Saqoosha/Canopy-MacroPad/case/out/choc/bottom.png

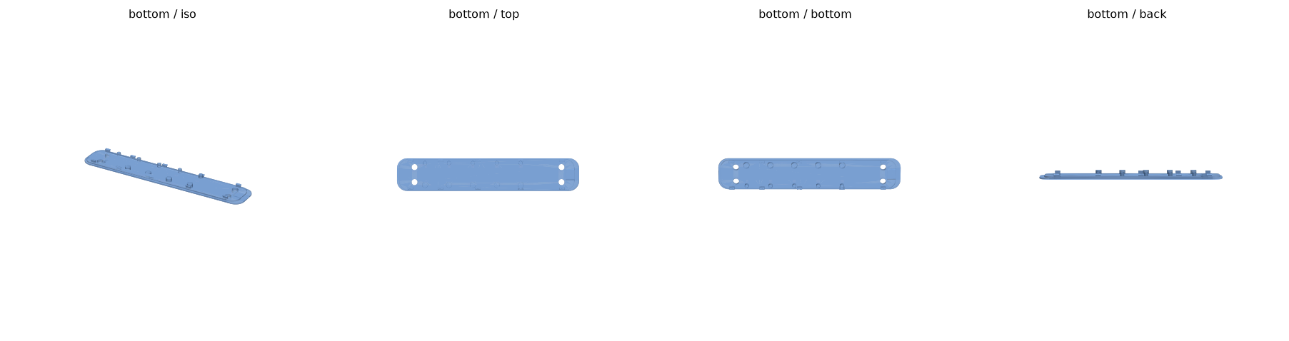
case/out/choc/bottom.png
