Saqoosha/Canopy-MacroPad/case/out/choc/coupon-clear.png

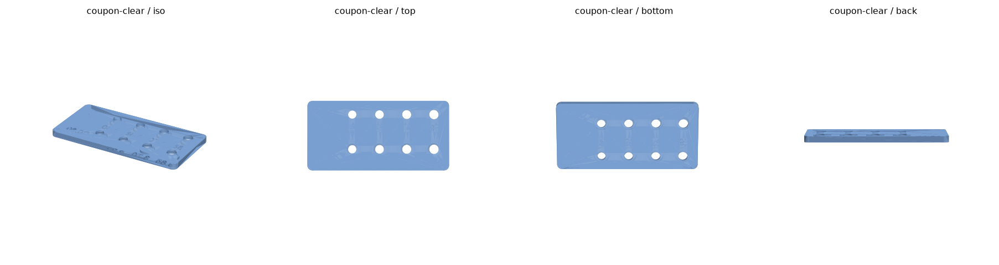
case/out/choc/coupon-clear.png
