Saqoosha/Canopy-MacroPad/case/out/choc/keycap.png

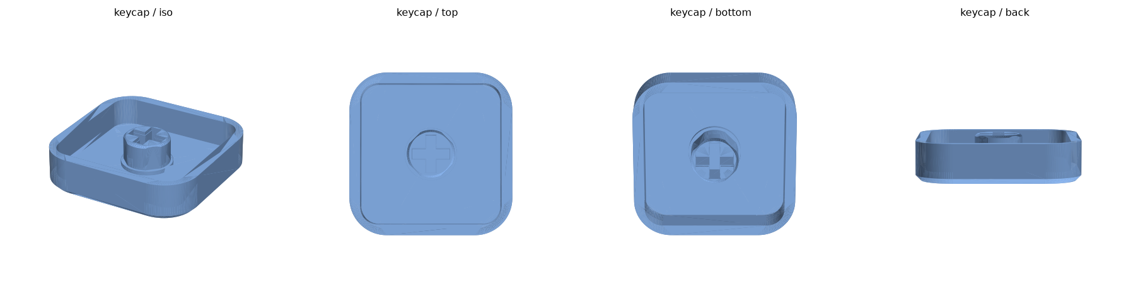
case/out/choc/keycap.png
