Saqoosha/Canopy-MacroPad/case/out/choc/product.png

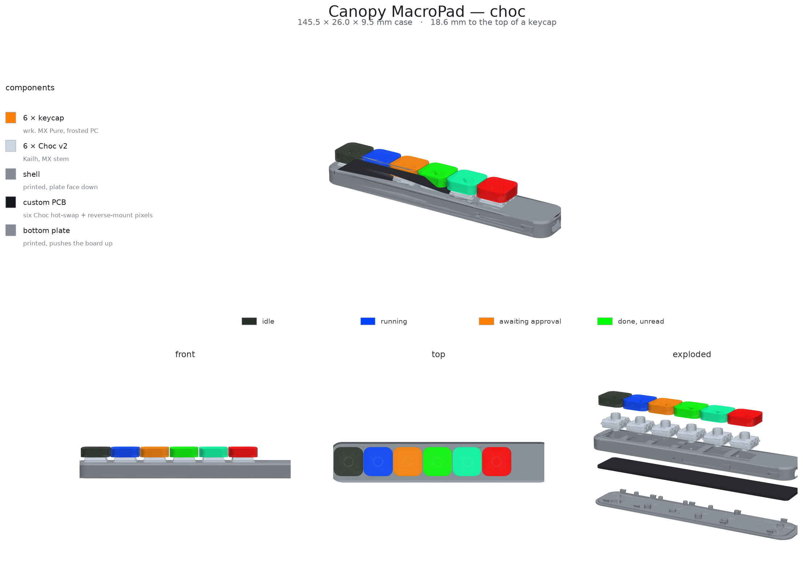
case/out/choc/product.png
