Saqoosha/Canopy-MacroPad/pcb/out/board-free.png

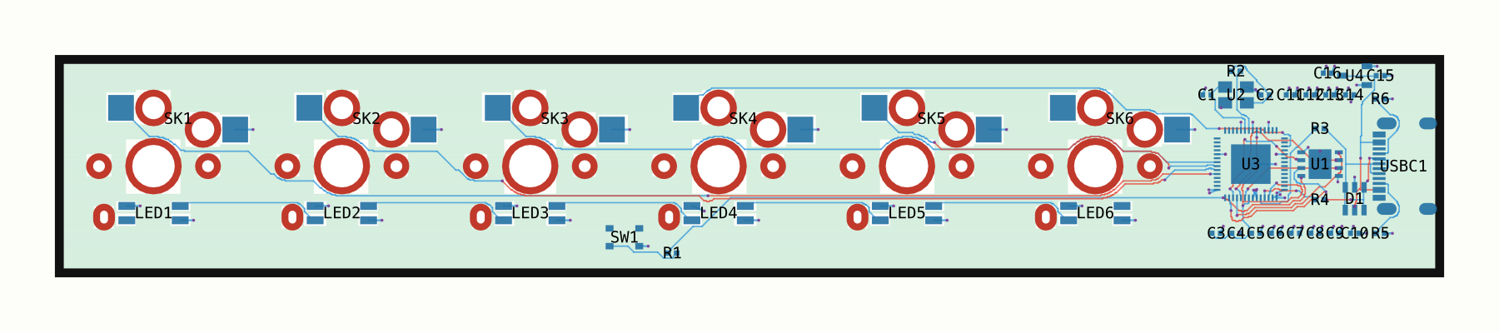
pcb/out/board-free.png
