Saqoosha/Canopy-MacroPad/pcb/out/board-large.png

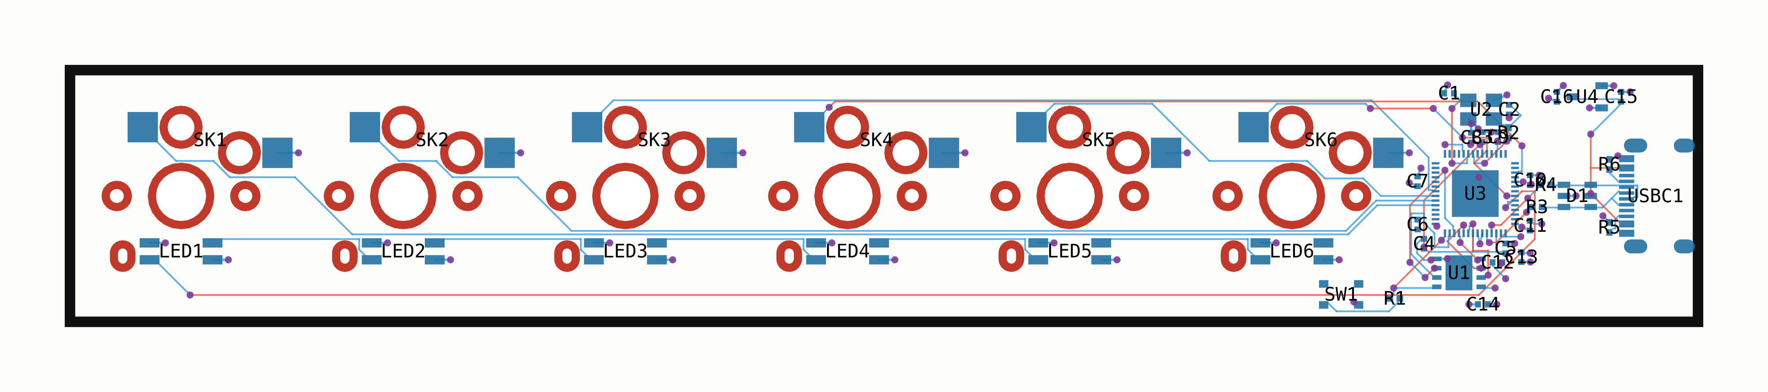
pcb/out/board-large.png
