Saqoosha/Canopy-MacroPad/pcb/out/mcu-crop.png

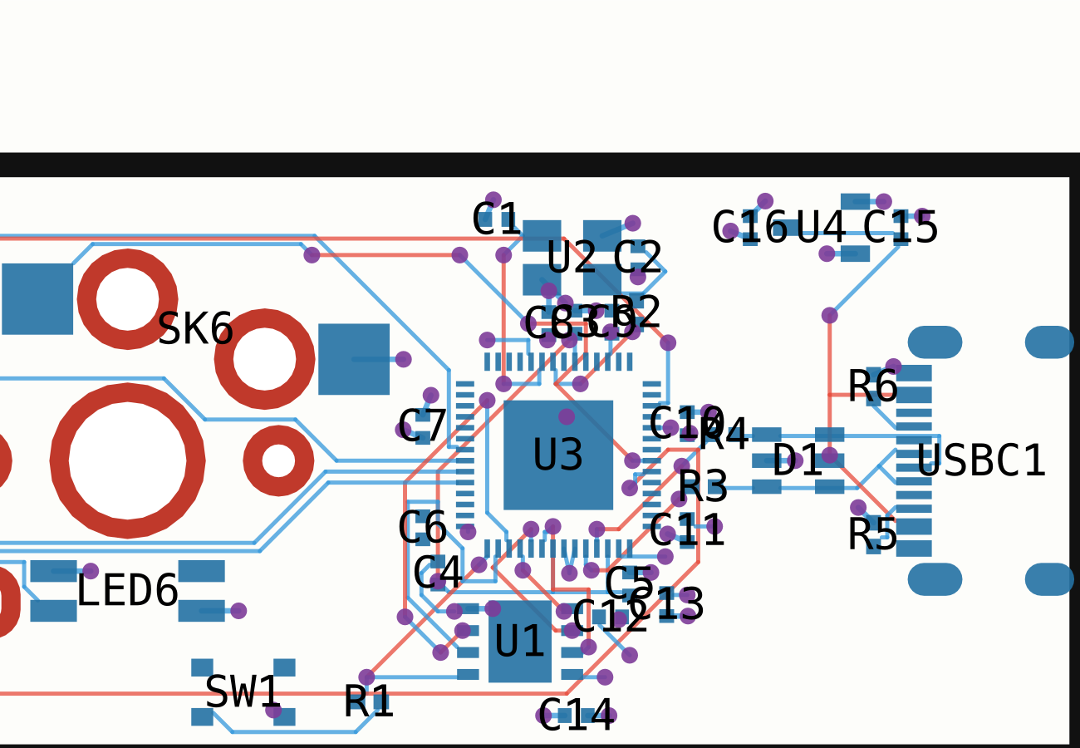
pcb/out/mcu-crop.png
