Saqoosha/Canopy-MacroPad/case/out/inline/coupon.step

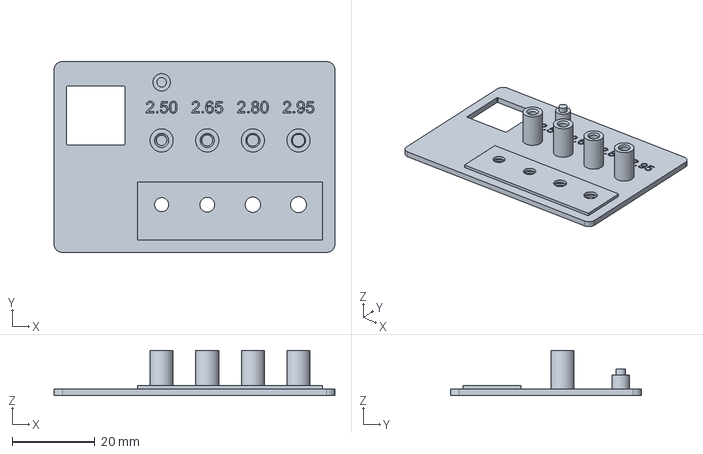
[picture p29: CAD file, 2026-08-14, an earlier design]
case/out/inline/coupon.step
67.8 x 46.0 x 10.9 mm
