Saqoosha/Canopy-MacroPad/case/out/stacked/shell.step

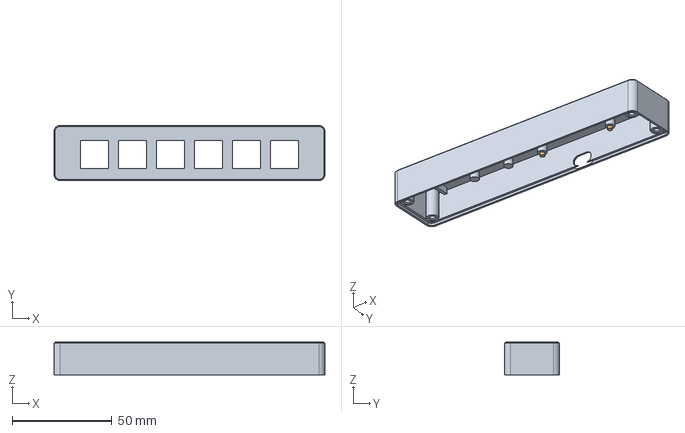
[picture p30: CAD file, 2026-08-14, an earlier design]
case/out/stacked/shell.step
135.7 x 27.6 x 16.3 mm
