Saqoosha/Canopy-MacroPad/docs/wiring/boards.jpg

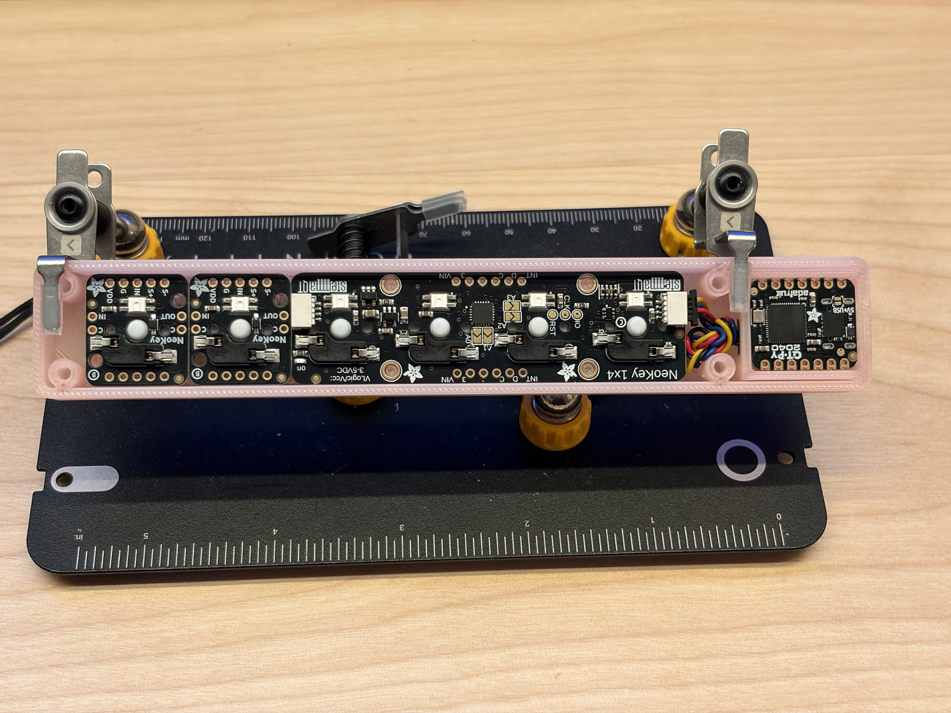
docs/wiring/boards.jpg
