Saqoosha/Canopy-MacroPad/firmware/code.py

"""Canopy MacroPad — main firmware.

The device is deliberately dumb: it reports key edges and paints the
colors it is told to paint. All meaning (which pane, which status, when
to pulse) lives in the host. That split is what lets the same wire
protocol survive the move to BLE later.

Wire protocol, line-delimited ASCII on usb_cdc.data.

  host -> device
    C <idx> <rrggbb>   set key idx to that color, e.g. `C 0 ff8000`
    S <idx> <rrggbb> [ms] [floor]
                       pulse that color, eased by `PULSE_CURVE`. `ms` is the full
                       period (min 100), `floor` is the percentage the
                       dip bottoms out at, 0-100: 0 reads as an alert,
                       50 as a slow breath that says "alive" without
                       asking for attention. Defaults: 2500 ms and 0.
                       Both are clamped silently.
    B <0-100>          global brightness
    X <ms>             crossfade duration for C and S, default 500
    P                  ping
    R                  reset: all keys off, immediately

  device -> host
    HELLO <ver> <keys> sent when a host opens the data port
    PONG <ver> <keys>  reply to P
    K <idx> <0|1>      key idx pressed (1) / released (0)
    ERR <msg>          a command could not be handled

`C` and `S` drop out-of-range key indices in silence; the host may paint
before it has learned the key count.

Every change of color or floor is crossfaded (except `R` and a host
disconnect, which are immediate), so a state change reads as
a state change and not as an alarm. Solid is modelled as a pulse whose
floor is 100%, which is what lets one interpolation cover all four
transitions -- solid to solid, solid to pulsing, pulsing to solid, and
pulsing to pulsing -- with no special cases.

**A pulsing key keeps its phase when only its color or floor changes.**
Resetting it would drop the breath back to its trough, and "the heartbeat
stopped" reads louder than "the urgency changed", which is the opposite
of what happened. Phase restarts only when a solid key starts pulsing, or
when the period itself changes.

Nothing else is written to the data port, and debug output goes to the
console port (plain `print`) which the host does not read — with one
exception. If `boot.py` did not take effect there is no data port, and
this falls back to the console, where protocol lines then share a stream
with the REPL banner and any tracebacks. The host is told so explicitly:
it receives `ERR no-data-cdc-check-boot-py` right after `HELLO`.
"""

import array
import math
import os
import sys
import time

import microcontroller
import usb_cdc

# adafruit_neokey and neopixel live in CIRCUITPY/lib, so they are the
# imports that can be missing -- a board flashed without the bundle, or
# with one for the wrong CircuitPython major. That is the same class of
# operator error as a missing Qwiic cable, which this firmware goes to
# real trouble to survive; at module scope they instead raise straight
# to the REPL and produce the silent brick everything else here is built
# to avoid. Imported inside the setup guards below instead.
#
# Two guards rather than one, because the two halves of the keypad fail
# independently now: a missing `neopixel` must not cost the NeoKey its
# LEDs, and a missing Qwiic cable must not cost the breakouts theirs.
NeoKey1x4 = None
NeoPixel = None

# 1: C / B / P / R
# 2: adds S (device-side eased pulse)
# 3: adds X, crossfades every C/S, and holds phase across a colour change
PROTOCOL_VERSION = 3

# Two boards run this file and they are not the same shape. The QT Py
# build is two Adafruit 4978 breakouts on GPIO plus a NeoKey on I2C; the
# custom PCB is six switches straight to GPIO and one six-pixel chain.
#
# They cannot share one pin table even though they share pin *numbers*.
# The PCB was laid out against the QT Py's broken-out GPIO on purpose, so
# the same eleven numbers are available on both -- but GPIO3 is the
# breakouts' pixel line on one board and KEY0 on the other. Every
# difference between the two devices lives in this table.
#
# Pins are GPIO **numbers**, resolved through `microcontroller.pin`, not
# names through `board`. `board` carries a per-build name table, and the
# QT Py's names are simply absent from the generic build the PCB runs --
# measured on the real board, not assumed: `[n for n in ('MOSI', 'MISO',
# 'SCK', 'TX', 'RX', 'SDA', 'SCL') if hasattr(board, n)]` returns `[]`
# there. `microcontroller.pin.GPIOn` is the chip's own numbering and is
# on every RP2040 build.
PROFILES = {
    # Adafruit QT Py RP2040. Keys 0-1 are the two breakouts, keys 2-5 the
    # NeoKey. All three GPIO sit on the QT Py's 3V/GND edge, so the
    # harness does not have to cross the board.
    "qtpy": {
        "gpio_keys": (4, 6),                # MISO, SCK
        "gpio_pixel": 3,                    # MOSI
        "pad_addresses": (0x30,),
        # 50 Hz, and no dithering at that rate -- see `PAINT_HZ`. Four of
        # this board's six pixels live behind seesaw, so a paint is I2C
        # traffic competing with the key scan for the same bus, and the
        # NeoKey's own comment upstream is about exactly that cost.
        "paint_hz": 50,
        # No dithering at 50 Hz: the table beside `DITHER` measures it as
        # worse than none.
        "dither": False,
    },
    # The custom PCB. Six switches on GPIO in the board's physical key
    # order, one chain of six pixels, and no I2C anywhere on the board --
    # so the whole I2C half below is skipped rather than failing.
    "pcb": {
        "gpio_keys": (3, 4, 6, 20, 5, 24),
        "gpio_pixel": 25,
        "pad_addresses": (),
        # 200 Hz, which is what buys the dithering below. Every pixel is
        # on one bit-banged GPIO chain: six of them is ~260 us per show,
        # so 200 Hz costs about 5% of wall time and no bus at all.
        "paint_hz": 200,
        # The loop achieves about 148 Hz of that with six keys pulsing, and
        # the flag is True on the strength of the lit board rather than of
        # the request: at that rate a 50/50 dither alternates near 74 Hz,
        # and every depth from 67% down was invisible on a static ladder.
        "dither": True,
    },
}

# Which profile, decided by which CircuitPython **binary** is running.
#
# That is not the detection this file forbids, and the difference is the
# whole reason this one is allowed to be automatic. Whether a breakout is
# *wired* is electrically unknowable -- an absent one and a present one
# nobody is pressing are both pulled high, with no readback on the pixel
# line and no capacitive sense on an RP2040 -- so that question was
# always a human's to answer. Which build you booted is a compile-time
# string, and there is no guess in reading it.
#
# `settings.toml`'s `MPAD_BOARD` overrides the table, and is the answer
# of record for a board whose build name is not in it. The PCB currently
# runs a stock `raspberry_pi_pico` build: a name it does not own, that an
# actual Pico would also answer to, and that stops matching the day the
# board gets a definition of its own.
#
# An unrecognised answer gets **no** fallback profile. A wrong guess
# renumbers every key silently, which is the one failure this file is
# built to prevent, so it comes up with no hardware at all and says so.
# Both strings were read off their own board's REPL, not taken from a
# board definition: `print(sys.implementation._build)` answers
# 'raspberry_pi_pico' on the built PCB and 'adafruit_qtpy_rp2040' on the
# QT Py. Worth re-reading after a CircuitPython upgrade, and the failure
# if one ever stops matching is the safe one -- that board comes up with
# `HELLO <ver> 0` and `ERR board ...` rather than with wrong pins, and
# `MPAD_BOARD` in settings.toml fixes it without a reflash.
BUILD_TO_PROFILE = {
    "adafruit_qtpy_rp2040": "qtpy",
    "raspberry_pi_pico": "pcb",
}
# Read through `getattr` because `_build` is a private attribute, and this
# line is at module scope where an AttributeError is the silent brick --
# CircuitPython stops `code.py`, the port goes quiet, and from the host
# that is indistinguishable from a board that never booted. A release that
# renames or drops it must land in the failure this file already has a
# path for: no profile, `ERR board`, and a device that still talks.
# `os.getenv` is not wrapped, deliberately -- it is public API, and
# guarding everything that could theoretically move is how a guard stops
# meaning anything.
_build = getattr(sys.implementation, "_build", None)
_forced = os.getenv("MPAD_BOARD")
BOARD_PROFILE = _forced or BUILD_TO_PROFILE.get(_build)
if BOARD_PROFILE in PROFILES:
    board_error = None
    _profile = PROFILES[BOARD_PROFILE]
else:
    board_error = "{} {!r} is not one of {}".format(
        "MPAD_BOARD" if _forced else "build",
        _forced or _build,
        "/".join(sorted(PROFILES)))
    _profile = {"gpio_keys": (), "gpio_pixel": None, "pad_addresses": (),
                "paint_hz": 50, "dither": False}

# The I2C addresses of the NeoKey boards, in physical left-to-right key
# order. This tuple is the single source of truth for how many boards
# exist -- deriving it the other way round (a count that slices a longer
# address list) silently clamps instead of failing. A second board needs
# its A0 jumper bridged on the back to answer 0x31. Empty on a board with
# no I2C keypad, and then nothing here is imported, addressed or reported
# on.
PAD_ADDRESSES = _profile["pad_addresses"]
KEYS_PER_PAD = 4
SEESAW_KEYS = KEYS_PER_PAD * len(PAD_ADDRESSES)

# The keys read straight off GPIO, in physical left-to-right order. They
# carry no seesaw, so there is nothing to address and nothing to
# enumerate -- which is why this is the half that cannot fail to come up.
# On the QT Py that is keys 0-1 and they come *before* the NeoKey's four;
# on the PCB it is all six and there is no other half.
#
# The switch wiring differs between the boards and only one of them has a
# margin worth watching. Each 4978 breakout puts its switch in series
# with a 1N4148 running SWITCHA to SWITCHC, and SWITCHC goes to ground,
# so a press pulls its input low *through the diode*. The forward drop at
# the ~55 uA an internal pull-up supplies is about 0.45 V, under the
# RP2040's 0.8 V V_IL but not by a wide margin: a key that reads
# permanently pressed is the symptom of that number being wrong, and an
# external pull-up is the fix. The PCB's switches go straight to ground
# with no diode in the way, so they have no such margin to lose.
#
# Resolved against `microcontroller.pin` inside the setup guard rather
# than here. A number missing from it would be an AttributeError at
# module scope, which is the silent brick again -- and a wrong-board
# flash is exactly when you want the serial half still talking.
GPIO_KEY_GPIO = _profile["gpio_keys"]
GPIO_PIXEL_GPIO = _profile["gpio_pixel"]
GPIO_KEYS = len(GPIO_KEY_GPIO)

# Index order is physical, left to right, and on the QT Py the case
# decided it rather than this file: the breakouts sit to the *left* of
# the NeoKey, for reasons of plug clearance and cable reach that
# `case/params.py` owns and states with its own numbers
# (`BREAKOUT_ORIGINS_LOCAL`). Restating one of them here is how a number
# gets carried away from what makes it true, so it is not restated.
#
# So on the QT Py the GPIO pair is 0-1 and the NeoKey is 2-5; on the PCB
# the GPIO six are 0-5 and `SEESAW_BASE` lands past the end and is never
# used. These two constants are the only place that knows which way round
# it goes.
GPIO_BASE = 0
SEESAW_BASE = GPIO_KEYS

# Derived from the profile, not from what enumerated at runtime. Key 2 is
# key 2 whether or not the NeoKey answered: the host maps index to pane,
# so letting the boards renumber when the Qwiic cable is out would
# quietly focus the wrong session.
#
# Both real profiles come to 6, by different sums -- 2 + 4 on the QT Py,
# 6 + 0 on the PCB -- so a missing NeoKey shows up as `HELLO <ver> 6`
# plus `ERR i2c ...` and the host paints keys 2-5 into a board that is
# not there. Writes to absent hardware are dropped in silence, the same
# way an out-of-range index already is.
#
# `HELLO <ver> 0` is reachable again, and means one thing only: this
# firmware does not know what board it is on. It arrives with `ERR board
# ...`, and it is the honest report -- claiming six keys that resolve to
# no pins would be a positive claim of health, which is worse than
# silence.
NUM_KEYS = SEESAW_KEYS + GPIO_KEYS

# Full brightness is genuinely painful to sit next to, but going too dim
# costs 8-bit steps: at 30% a deep pulse has only a handful of distinct
# values near its floor and visibly stalls there. 60% measured as the
# point where the fade stays smooth without being glaring. The host can
# override this at runtime with `B`.
#
# Measured on a lit board, and the number stands -- but for a reason the
# original note did not have. `DITHER` buys steps back above
# `DITHER_FLOOR`, and separately the board says a one-level step stops
# being visible around value 2 anyway. So the low end is not as bad as
# this comment once implied, and 60 is no longer a floor forced by
# quantisation. It is still what idle's white balance was measured at,
# which is the reason not to move it casually.
DEFAULT_BRIGHTNESS = 0.6

# All timing is integer nanoseconds. `time.monotonic()` returns a float
# whose precision decays with uptime -- on a single-precision build the
# step near `now` grows past both thresholds below in a day or two --
# 15 ms is the ulp somewhere past 2^17 seconds -- and this is a device
# that lives plugged into a desk. The failure
# is silent and awful: the debounce window stops measuring anything, so
# one press reports as several and the wrong pane gets focused.
DEBOUNCE_NS = 15_000_000       # 15 ms

# How often the LEDs are repainted, and it is a per-board number because
# it buys different things on the two boards. It is the pulse's sample
# rate, and -- at 200 Hz and above -- the carrier the dithering below
# rides on.
#
# **It is a request, not the achieved rate.** `POLL_INTERVAL_S` is 5 ms so
# 200 Hz is the arithmetic ceiling, but the loop measured **148 Hz** with
# six keys pulsing -- a 26% shortfall. Which is why whether to dither is a
# separate field in the profile rather than a comparison against this
# number: a comparison would be deciding on a rate the board does not
# reach. What was actually judged, on the lit board at 148 Hz, is recorded
# beside each profile's flag.
PAINT_HZ = _profile["paint_hz"]
PULSE_STEP_NS = 1_000_000_000 // PAINT_HZ
# Temporal dithering is only switched on where the paint rate can carry
# it, and 200 Hz is not a round number -- it is where the measurement
# crosses over. Error-diffusing at 50 Hz is *worse than not dithering*,
# because the dither's own alternation then lands inside the band the eye
# sees as flicker rather than above it. Simulated against the real
# quantiser, error energy in the visible 5-30 Hz band, in LSB rms, for a
# gamma-2.0 breath at floor 0.15:
#
#     brightness   today@50   dither@50   @100    @200    @400
#     0.10            0.254      0.396   0.230   0.084   0.031
#     0.15            0.237      0.378   0.237   0.075   0.029
#     0.60            0.347      0.390   0.198   0.082   0.037
#
# So 50 Hz loses, 100 Hz draws, and 200 Hz wins by 3x. A board that
# cannot afford 200 Hz must not dither at all, which is why this is a
# threshold and not a preference.
# Read from the profile rather than derived as `PAINT_HZ >= 200`, which is
# what this line used to say and was a small lie: `PAINT_HZ` is the rate
# the loop *asks* for and the PCB achieves about 148 of it, so the
# comparison passed on a board that misses its own stated bar. The
# threshold above is still the reason each flag is set the way it is; what
# changed is that the flag records a decision instead of pretending to
# derive one, and the profile carries the measurement beside it.
DITHER = _profile["dither"]

# Below this output value a channel is rounded rather than dithered, and
# it is the second half of the threshold above -- 200 Hz is necessary and
# is not sufficient. Both numbers came off the lit board, on static
# ladders where nothing but the dither could move.
#
# What the eye is judging is the dither's *depth*, one level as a share
# of the light there, against the rate its pattern happens to run at.
# Error diffusion holds one value for 1/fraction frames, so at 200 Hz a
# fraction of 0.1 alternates at 20 Hz. Painting faster raises that -- 400
# Hz would give 40 Hz -- but then a fraction of 0.05 alternates at 20 Hz
# instead. The rate cannot be bought out of this, because the fraction
# can always be smaller.
#
#   depth   1 LSB on   at 100 Hz   at 20 Hz
#   100%    value 1    calm        flickers
#    50%    value 2    calm        flickers
#    33%    value 3    calm        faint, still there
#    20%    value 5    calm        calm
#    11%    value 9    calm        calm
#
# So 5 is where the worst rate stops being visible. 4 is the untested
# boundary and 5 is inside it.
#
# **That derivation assumes the LED is linear, and it is not.** Keys held at
# 0/1/2/3/4/5 side by side on the real board: 0 to 1 is a different world, 1
# to 2 is plainly visible, and 2/3/4/5 cannot be told apart at all. Only the
# first two steps are visible, so 5 is conservative rather than correct --
# and the arithmetic above, which reasons about "one level as a share of the
# light", is answering a question the part does not obey. Left at 5 because
# nothing in service goes near it (see below), not because the number was
# re-derived. What this buys back is everything above
# it; below it the levels were never recoverable by any temporal trick,
# and rounding at least fails quietly. A dither there is not a smoother
# value, it is a light switching on and off.
DITHER_FLOOR = 5.0

# Adds roughly 5 ms plus the scan and paint themselves on top of the
# 15 ms debounce, so a press reaches the host in ~20 ms. The debounce
# dominates; this only decides how much is added to it.
POLL_INTERVAL_S = 0.005

# The pulse lives here rather than on the host. A square blink is one
# command per half period and could sit on the host happily; a sine fade
# is ~50 updates a second, which is a silly thing to push down a wire and
# would stutter on any host hiccup. Keeping it local also means the pulse
# is already where it has to be when this moves to BLE.
#
# A pulse is timed from the moment its command arrives, so a key entering
# a state fades up from its floor and the transition itself is visible.
# An earlier revision also added a fixed per-key phase offset, to stagger
# keys told to pulse in the same instant. The two are not compatible: an
# offset that is non-zero at t=0 is exactly a key that does not start at
# its floor, and with four keys it put key 2 at full brightness on its
# very first frame. Starting at the floor won, because the key it broke
# is whichever one is holding the approval state -- nothing here maps a
# key index to a pane state, so it could be any of them. Keys whose states change at different
# moments still drift apart on their own.
#
# 2.5 s, chosen on a lit board against 2/3/4/5/6/8 s shown on the six keys
# at once. 2 s is 30 breaths a minute, outside the 12-20 a resting adult
# does, and a photodiode capture of a real MacBook sleep light measured
# about 12; this lands at 24, which is slower than the 2 s it replaces and
# still quick enough that a deep pulse reads as a request rather than as
# scenery. Every state uses it and only the floor changes.
#
# The host sends its own period with every `S`, so this is what a host that
# omits one gets, not what the pad normally runs. Canopy sends 2500.
DEFAULT_PULSE_PERIOD_MS = 2500
# `PULSE_GAMMA` shapes nothing any more. It is the exponent of the cosine
# family the curve below replaced, kept because that family's runner-up is
# one line away and because the number itself was earned: 1.5, picked on a
# lit board from a sweep of 1.0/1.2/1.4/1.6/1.8/2.0 carried on the six keys
# at once.
#
# What that sweep settled, and it is worth keeping because the first
# explanation of it was half wrong. A raw sine (gamma 1.0) reads as "the
# bottom is short and the top is long" -- it lingers exactly where the eye
# is least able to see a change. Gamma 2.0 reads as a pause at the bottom,
# because level-minus-floor goes as t^4 there against t^2 at 1.0, so the
# lowest 1% of the swing lasts 410 ms of a 2 s breath instead of 128. Both
# ends are wrong and the answer was between them.
#
# The old note in this place blamed that pause on there being few 8-bit
# levels at low brightness. Both facts are real and they are not cause and
# effect: the freeze is the two **meeting**, 410 ms of dwell spanning under
# 2 LSB. Dithering is the right instrument for that half and the note was
# right to name it; what it got wrong was calling it cheap. It costs a 4x
# paint rate (`DITHER`), below 200 Hz it makes the pulse worse, and below
# `DITHER_FLOOR` no rate saves it at all.
#
# And the whole quantisation half turned out not to happen in service. The
# deepest breath Canopy sends bottoms out at 7.7 of 255 in its faintest lit
# channel, where a one-level step stopped being visible around 2 -- measured
# on the board, keys held at 0/1/2/3/4/5 side by side. Everything above was
# found at brightness 15 with a floor of 0, which is outside the envelope
# the pad is ever driven in.
PULSE_GAMMA = 1.5

# The breath, precomputed at boot. Not from `PULSE_GAMMA` -- that constant
# belongs to the cosine family this replaced; see its own note above.
#
# The shape is `exp(sin)`: `(e^sin(x) - 1/e) / (e - 1/e)`, normalised and
# phase-shifted to start at its minimum. Narrow peak, wide trough -- the
# dwell sits at the bottom of the breath where a raw sine puts it at the
# top, and the top is exactly where the eye is least able to see a change.
# Traced to a 2010 comment by Adam Shea, popularised by Sean Voisen in
# 2011; Shea's stated reason was correcting the log response of
# LED->eye->brain rather than modelling breathing, and the curve is
# exactly time-symmetric about its peak whatever the folklore says.
#
# Chosen on a lit board against five others shown side by side on the six
# keys at once -- a plain triangle, FastLED's `quadwave` and `cubicwave`,
# `sine^1.5`, and the Gaussian fitted to a real MacBook sleep light -- all
# sharing colour, floor, phase and brightness so only the curve differed.
# A gamma sweep over the cosine ran the same way first: 1.0 read as "the
# bottom is short and the top is long", 2.0 as a pause at the bottom, and
# 1.5 was the best of that family before this beat it.
#
# `PULSE_GAMMA` no longer shapes anything -- it belongs to the cosine
# family this replaced. It is kept only because `sine^1.5` is one line
# away and was the runner-up:
#
#     _raw = [((1 - math.cos(2 * math.pi * _i / _CURVE_STEPS)) / 2)
#             ** PULSE_GAMMA for _i in range(_CURVE_STEPS)]
#
# The **table** is a speed change with no effect on the shape. `math.cos`
# and `** PULSE_GAMMA` ran once per key per frame and measured as the
# largest single cost in the loop, and the index is integer arithmetic so
# the float divide goes with them.
#
# 512 is not a round number, it is the smallest power of two finer than a
# frame. A table adds a visible stair only when its steps are coarser than
# the frames sampling it, so the comparison that decides the size is
# against the loop rate rather than against the eye:
#
#     table    step     biggest jump      steps per frame
#     entries  apart    between entries   at 148 Hz (6.76 ms)
#      256     7.81 ms      3.61 LSB           0.9   <- coarser than a frame
#      512     3.91 ms      1.81 LSB           1.7
#
# The biggest change one frame to the next is 3.13 LSB at 148 Hz, so at 512
# the table's own step is already the smaller of the two and contributes no
# hold the frames did not already have. At 256 it is the larger, and would.
#
# Written out as literals this table **hard-faulted CircuitPython into
# safe mode** -- 1536 floats of source, and it was the parser rather than
# the data: measured on the board afterwards, the array costs ~2 KB of a
# free 162 KB and a lookup is 21 us. Build it, never paste it.
_CURVE_STEPS = 512
_E = math.e
_raw = [(math.exp(math.sin(2 * math.pi * _i / _CURVE_STEPS - math.pi / 2)) - 1 / _E)
        / (_E - 1 / _E) for _i in range(_CURVE_STEPS)]
_span = max(_raw) - min(_raw)
PULSE_CURVE = array.array("f", [(_v - min(_raw)) / _span for _v in _raw])
# The cosine starts at its minimum, and the whole phase rule depends on it:
# a key that begins pulsing has to fade up rather than snap to full. That
# is a property of the expression above, so it is asserted rather than
# assumed -- a curve edited to start anywhere else breaks a promise made
# in `set_pulse`, and nothing else in this file would notice.
assert PULSE_CURVE[0] < 0.02

# How long a color or floor change takes to complete. An instant switch
# reads as "something just happened", but most transitions are a session
# moving from one continuous state to the next -- so an abrupt change
# makes the pad overstate the event. 500 ms is slow enough to read as a
# transition rather than a glitch, fast enough not to lag the session.
DEFAULT_CROSSFADE_NS = 500_000_000
# One fat-fingered X must not look like a hung device.
MAX_CROSSFADE_MS = 10_000

# A host that never sends a newline would otherwise grow the receive
# buffer until the heap gives out -- the only unbounded allocation in a
# loop that is otherwise allocation-free. Longest legal line is ~24 bytes.
MAX_LINE_BYTES = 256

# How many consecutive failed I2C scans before the keypad is declared
# gone on the console. One or two is bus noise; a run of them is a cable.
I2C_FAIL_LIMIT = 20


# `board.STEMMA_I2C()` is what raises when the Qwiic cable is missing:
# the I2C pull-ups live on the NeoKey board, so without it the bus check
# fails before any NeoKey1x4 is constructed. That must not kill the whole
# device. With the serial half still up, a host that receives
# `HELLO <ver> 0` learns "the pad is plugged in but has no keypad
# attached", which is a diagnosable state. Dying here instead leaves a
# port that never answers, indistinguishable from a board that failed to
# boot at all.
#
# Each board is then initialised separately so a second board with an
# unbridged A0 jumper -- the likeliest wiring mistake once there are two
# -- degrades to "one board works" instead of "no keypad at all".
# `pads` is (base index, board) so the base survives a board that did
# not answer. `pixel_groups` is (pixel object, base index, count) for
# every run of keys that shares one strip of pixels -- one per NeoKey
# board, plus one for the whole breakout chain. Both a NeoKey's
# `pad.pixels` and a `neopixel.NeoPixel` are adafruit_pixelbuf.PixelBuf
# subclasses, so they take the same `[i] = rgb`, `.show()`, `.fill()`
# and `.brightness`, and one routing table covers both kinds.
pads = []
pixel_groups = []
pad_errors = []
i2c = None
# Skipped whole on a board with no I2C keypad, and the skip is the exact
# mirror of the GPIO one below. Running it anyway would import
# `adafruit_neokey` and call `board.STEMMA_I2C()` on a device that has
# neither, so every connect would carry an `ERR i2c setup ...` about
# hardware the board was never built with -- forever, and about a fault
# that cannot be fixed. That is precisely the noise this firmware refuses
# to emit, and a host told to expect it learns to ignore the real one.
if PAD_ADDRESSES:
    try:
        import board

        from adafruit_neokey.neokey1x4 import NeoKey1x4
        i2c = board.STEMMA_I2C()
    except Exception as err:  # noqa: BLE001 - a missing lib and a missing
        # cable arrive here identically, and both must leave the serial
        # half alive so the host is told rather than left staring at a
        # dead port.
        i2c = None
        pad_errors.append("setup {}: {}".format(type(err).__name__, err))
if i2c is not None:
    for slot, addr in enumerate(PAD_ADDRESSES):
        # The base index comes from the slot, not from how many boards
        # answered. Appending in arrival order means that with two
        # addresses configured and the first one silent, the second
        # board's keys take the first board's indices -- the same silent
        # renumbering the GPIO half is kept static to avoid.
        base = SEESAW_BASE + slot * KEYS_PER_PAD
        try:
            pad = NeoKey1x4(i2c, addr=addr)
            # NeoKey1x4 leaves auto_write on, which turns every single
            # pixel assignment into a full buffer transmit plus a SHOW
            # over seesaw. During a pulse that is one transaction per key
            # per step -- four times the bus traffic needed, competing
            # with the key scan for the same bus. Batch instead: write
            # the pixels, then show once per pad per tick.
            pad.pixels.auto_write = False
            # Left at 1.0 and scaled in `paint()` instead. Not a style
            # choice: pixelbuf scales with `(v * int(b*256)) // 256`, an
            # integer floor *after* this file has already rounded to 8
            # bits, so at brightness 0.30 seventy per cent of the values
            # this file can express collapse onto a byte something else
            # already occupies. Dithering upstream of that is provably a
            # no-op -- simulated at 0.30 and below it reproduces today's
            # output frame for frame. One quantisation, owned here.
            pad.pixels.brightness = 1.0
            pad.pixels.fill(0x000000)
            pad.pixels.show()
            pads.append((base, pad))
            pixel_groups.append((pad.pixels, base, KEYS_PER_PAD))
        except Exception as err:  # noqa: BLE001
            pad_errors.append("0x{:02x} {}: {}".format(
                addr, type(err).__name__, err))

# The GPIO half comes up in two guards, because it fails in two ways.
# The pins are core CircuitPython and cannot go missing; `neopixel` is a
# file on the drive exactly like adafruit_neokey. Losing the library
# must not cost these two keys their presses, so the switches are built
# first and separately -- the half that needs nothing stays working when
# the half that needs something does not.
#
# Skipped whole when the profile has no GPIO keys, and the skip is not
# cosmetic: `NeoPixel(pin, 0)` is a zero-length strip, which is either
# an exception -- and then such a board reports `ERR gpio pixels` on
# every single connect, forever, about hardware it was never built with
# -- or an empty group nothing will ever write to. Neither is worth
# carrying, and the first would teach a host to ignore that error.
gpio_switches = []
gpio_errors = []
if GPIO_KEYS:
    try:
        import digitalio

        for num in GPIO_KEY_GPIO:
            pin = getattr(microcontroller.pin, "GPIO{}".format(num))
            switch = digitalio.DigitalInOut(pin)
            switch.switch_to_input(pull=digitalio.Pull.UP)
            gpio_switches.append(switch)
    except Exception as err:  # noqa: BLE001
        gpio_errors.append("keys {}: {}".format(type(err).__name__, err))
    try:
        from neopixel import NeoPixel

        # GRB is the WS2812 family's wire order and what the NeoKey's
        # seesaw driver already assumes, so the breakouts carrying the
        # same NEO3535_REVERSE part should match, and so do the PCB's
        # SK6812MINI-E. If these keys come up with red and green swapped
        # while any NeoKey's look right, this is the line -- it is a
        # property of the LED, and neither the .brd files nor the PCB's
        # schematic states it.
        gpio_pixels = NeoPixel(
            getattr(microcontroller.pin, "GPIO{}".format(GPIO_PIXEL_GPIO)),
            GPIO_KEYS,
            # 1.0 for the reason given at the NeoKey's own brightness
            # line: the scaling happens in `paint()` so there is one
            # quantisation rather than two stacked.
            auto_write=False, brightness=1.0,
            pixel_order="GRB")
        gpio_pixels.fill(0x000000)
        gpio_pixels.show()
        pixel_groups.append((gpio_pixels, GPIO_BASE, GPIO_KEYS))
    except Exception as err:  # noqa: BLE001
        gpio_errors.append("pixels {}: {}".format(type(err).__name__, err))
# Two variables on purpose. `boot_i2c_error` is what setup found and
# never changes; `i2c_error` is what is true *now*, so the connect
# branch reports the current state instead of a snapshot taken before
# the cable was knocked loose. Without that split, a host reconnecting
# after a runtime bus loss is greeted with a clean HELLO and a key count
# the device can no longer honour -- worse than silence, because it is a
# positive claim of health.
#
# The key count in HELLO stays at its startup value even then. Resizing
# eight parallel per-key lists mid-loop is the one hazard this shape
# genuinely has, and it is not worth taking for a rare fault when the
# accompanying ERR already says the keypad is gone.
boot_i2c_error = "; ".join(pad_errors) or None
i2c_error = boot_i2c_error
# What the GPIO half found wrong with itself, reported next to the I2C
# faults so a missing `neopixel` is diagnosable instead of being two
# dark keys. There is no runtime twin of this one: a bus can be
# unplugged mid-session, a soldered pin cannot.
gpio_error = "; ".join(gpio_errors) or None

# Per key, one appearance model for both solid and pulsing: a colour and
# a floor, where floor 1.0 means the sine contributes nothing and the key
# is simply lit. That single representation is what lets one crossfade
# cover all four transitions -- solid->solid, solid->pulsing,
# pulsing->solid, pulsing->pulsing -- with no special cases.
#
# `from_*` is the appearance the running crossfade started from, `to_*`
# is where it is heading, and `fade_started` is when. Separate lists
# rather than tuples: nothing here is ever resized, and comparing whole
# scalars avoids the field-order coupling a packed tuple invites.
from_rgb = [0x000000] * NUM_KEYS
from_floor = [1.0] * NUM_KEYS
to_rgb = [0x000000] * NUM_KEYS
to_floor = [1.0] * NUM_KEYS
fade_started = [0] * NUM_KEYS
# The period in **milliseconds**, which is what the wire already sends, and
# the phase as a **position** inside it rather than the timestamp the breath
# started at. Both stay small integers for ever, and that is the whole
# reason for the shape.
#
# `monotonic_ns()` passes MicroPython's 30-bit small-integer boundary within
# a second of boot, so every expression touching it allocates. The curve
# index used to be
# `(now - pulse_started[i]) % period_ns[i] * _CURVE_STEPS // period_ns[i]`
# -- four big-integer operations per key per frame, and replacing just that
# expression with a small-integer counter took the loop from 142 Hz to 180
# with six keys pulsing. 236 us a key.
#
# Milliseconds counted from boot would not have fixed it: `now // 1_000_000`
# crosses the same boundary after about twelve days, and this device lives
# plugged in for weeks -- so that version works on the bench and stops
# working in service, silently, months later. A position advanced each frame
# and reduced modulo the period is bounded by the period itself and never
# grows.
period_ms = [DEFAULT_PULSE_PERIOD_MS] * NUM_KEYS
phase_ms = [0] * NUM_KEYS
# Nanoseconds the frame delta has not yet handed to `phase_ms`, and the
# timestamp it was last measured from. Carrying the remainder rather than
# dropping it is not tidiness: truncating each frame's delta would run every
# breath slow by the truncation -- 0.6% at a 7.042 ms frame and 11% at a
# 6.76 ms one, the worst of the four rates check 10 tests -- and a rate
# error never corrects itself.
_phase_carry_ns = 0
_phase_last_ns = 0
# Last value actually pushed to each pixel. None means "nothing written
# yet", which is distinct from black, so the startup fill does not poison
# the cache. Holds the *logical* color: adafruit_pixelbuf re-renders from
# its unscaled buffer when brightness changes, so `B` still lands on
# solid keys without invalidating this.
# Holds the *hardware* byte triple -- what pixelbuf will transmit --
# because this file now applies the global brightness itself. It used to
# hold the logical colour and lean on pixelbuf re-rendering its unscaled
# buffer when `.brightness` changed; with the scaling moved here that no
# longer happens, so `B` has to invalidate instead. `set_brightness`
# does, and the settled-solid skip in the render loop tests this list so
# that the invalidation actually reaches a key that has stopped moving.
last_rgb = [None] * NUM_KEYS
# Which pixel groups have writes waiting for a show().
group_dirty = [False] * len(pixel_groups)

# The global brightness, 0.0-1.0, applied in `paint()`. The host owns it
# through `B`.
brightness = DEFAULT_BRIGHTNESS
# Per-channel dither residue, three floats per key, flat so the hot path
# indexes instead of allocating. Carrying the fraction a byte cannot hold
# into the next frame is the whole mechanism: the output alternates
# between the two bytes either side of the true value at whatever duty
# makes the time-average land on it, which is why the mean tracks the
# ideal to about 0.002 LSB. Only meaningful above `DITHER`'s threshold --
# below it the alternation is slow enough to read as flicker.
dither_err = [0.0] * (NUM_KEYS * 3)

serial = usb_cdc.data
using_fallback_port = serial is None
if using_fallback_port:
    serial = usb_cdc.console

# `connected` only means the host asserted DTR -- it says nothing about
# whether the host is *reading*. A host that opens the port and then
# stops draining (suspended, at a debugger breakpoint, App Nap) fills the
# CDC endpoint, and the default write_timeout of None then blocks
# forever, freezing the one loop that scans keys and paints LEDs. A
# bounded timeout stops the stall. Note what it does *not* do:
# CircuitPython's write returns a short count rather than raising on
# timeout, so the result is a truncated line, not a dropped one. The
# fragment glues onto the next message, so the host loses two lines and
# resyncs at the newline after them.
serial.write_timeout = 0.05


def write_line(text):
    """Write one protocol line. True only if it actually left.

    Covers two cases the loop must survive: no host has the port open,
    and a host has it open but is not draining it. Callers that commit
    state on the strength of a message -- the key scan does -- must check
    the result, or the device ends up believing it said something it
    never said.
    """
    if not serial.connected:
        return False
    try:
        # A newline anywhere in the payload would split one message into
        # two and hand the host a fragment it cannot parse. This is the
        # single choke point, so sanitising here covers every caller.
        serial.write(text.replace("\n", " ").replace("\r", " ").encode() + b"\n")
        return True
    except Exception:  # noqa: BLE001 - a dropped line must not stop the loop
        return False


def write_pixel(idx, rgb):
    """Stage a color for one key, skipping unchanged writes.

    Cheap insurance rather than a hot-path win: a bright pulse really
    does change value on nearly every step. What this elides is the
    repeated identical commands a host is explicitly invited to send, and
    every step of a dark or shallow pulse, where the 8-bit output does
    repeat. Call `flush_pixels()` to push staged writes to the hardware.
    """
    if last_rgb[idx] == rgb:
        return
    for g in range(len(pixel_groups)):
        pixels, base, count = pixel_groups[g]
        if not base <= idx < base + count:
            continue
        # Hardware first, bookkeeping second. The other order looks
        # harmless until an I2C fault raises between them: the cache then
        # claims the key was painted, every later write of that value is
        # elided as redundant, and a settled solid key -- which the
        # render loop skips -- keeps the old colour until the host
        # happens to change it. Including through `all_off()`, which is
        # the frozen orange key the disconnect handler exists to prevent.
        pixels[idx - base] = rgb
        last_rgb[idx] = rgb
        group_dirty[g] = True
        return
    # No hardware behind this key -- a NeoKey that did not answer, or a
    # `neopixel` that would not import. Drop it the way an out-of-range
    # index is dropped, and leave the cache alone so that nothing is
    # remembered about a pixel that was never written.


def flush_pixels():
    """Push staged writes to hardware. Returns the first error, or None.

    Guarded per group rather than inside the loop's single try. The
    groups fail independently: a bus that cannot paint the NeoKey must
    not stop the breakout chain painting, which is the whole reason keys
    0 and 1 hang off GPIO. That holds for every I2C fault with the cable
    still in it. It does not hold for the cable itself -- the built unit
    draws the breakouts' VDD off the NeoKey's header, so an unplugged
    cable takes their pixels with it whatever this function does.
    """
    first_err = None
    for g in range(len(pixel_groups)):
        if not group_dirty[g]:
            continue
        try:
            pixel_groups[g][0].show()
            group_dirty[g] = False
        except Exception as err:  # noqa: BLE001 - the caller reports it
            if first_err is None:
                first_err = err
    return first_err


def invalidate_pixels():
    """Forget what the hardware is showing, so the next tick repaints.

    Called after an I2C failure: the write cache cannot be trusted about
    anything that may have been half-applied, and a settled solid key
    would otherwise never be written again.
    """
    for i in range(NUM_KEYS):
        last_rgb[i] = None
    for i in range(len(group_dirty)):
        group_dirty[i] = True
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
